nullvalue0/S100MotherboardV5/rescue-backup/S100-Backplane-2023-11-26-14-36-15.sch

## KiCad design rescue-backup/S100-Backplane-2023-11-26-14-36-15.sch (2023-12-12)

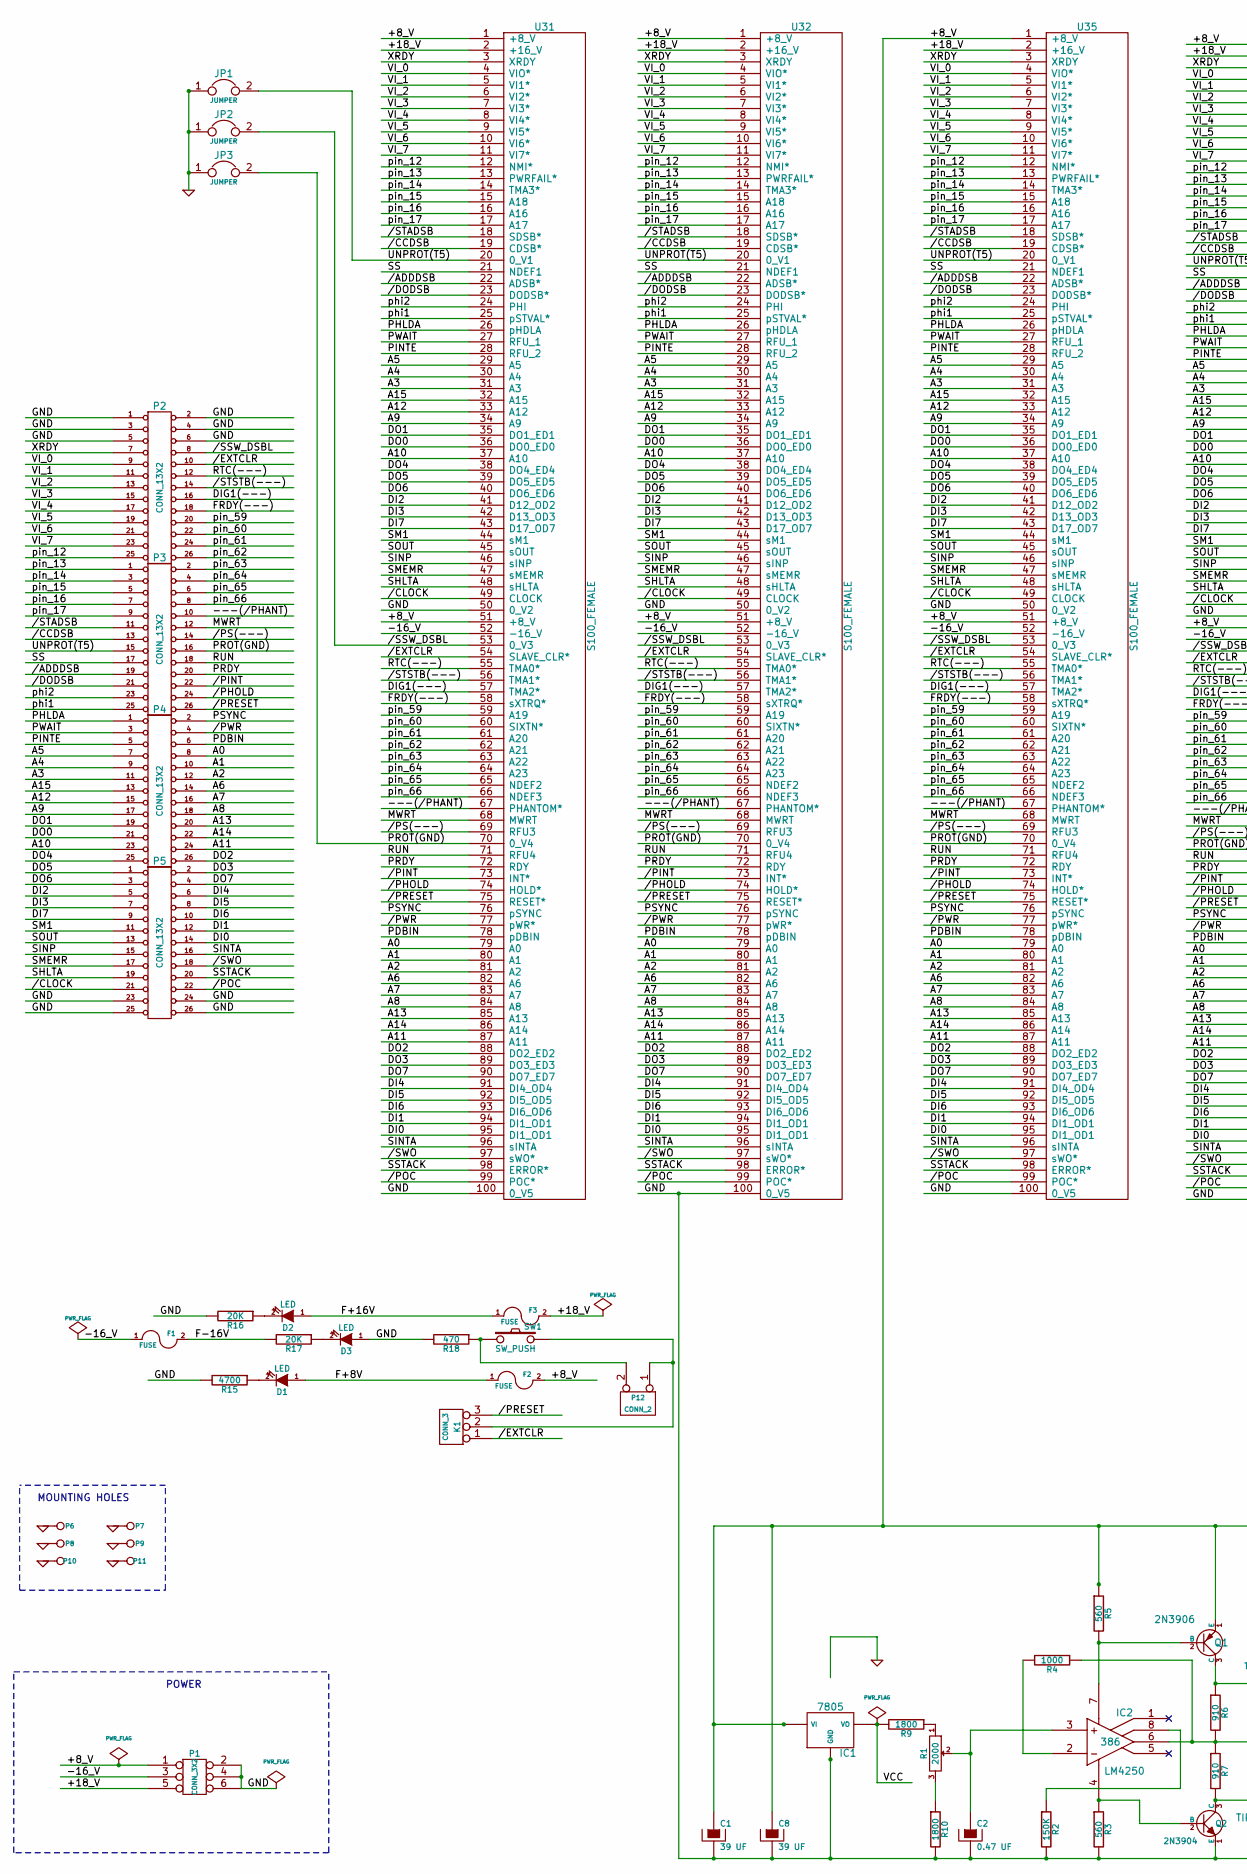
[picture p10: schematic S100-Backplane-2023-11-26-14-36-15.sch, part in row 1, column 1]

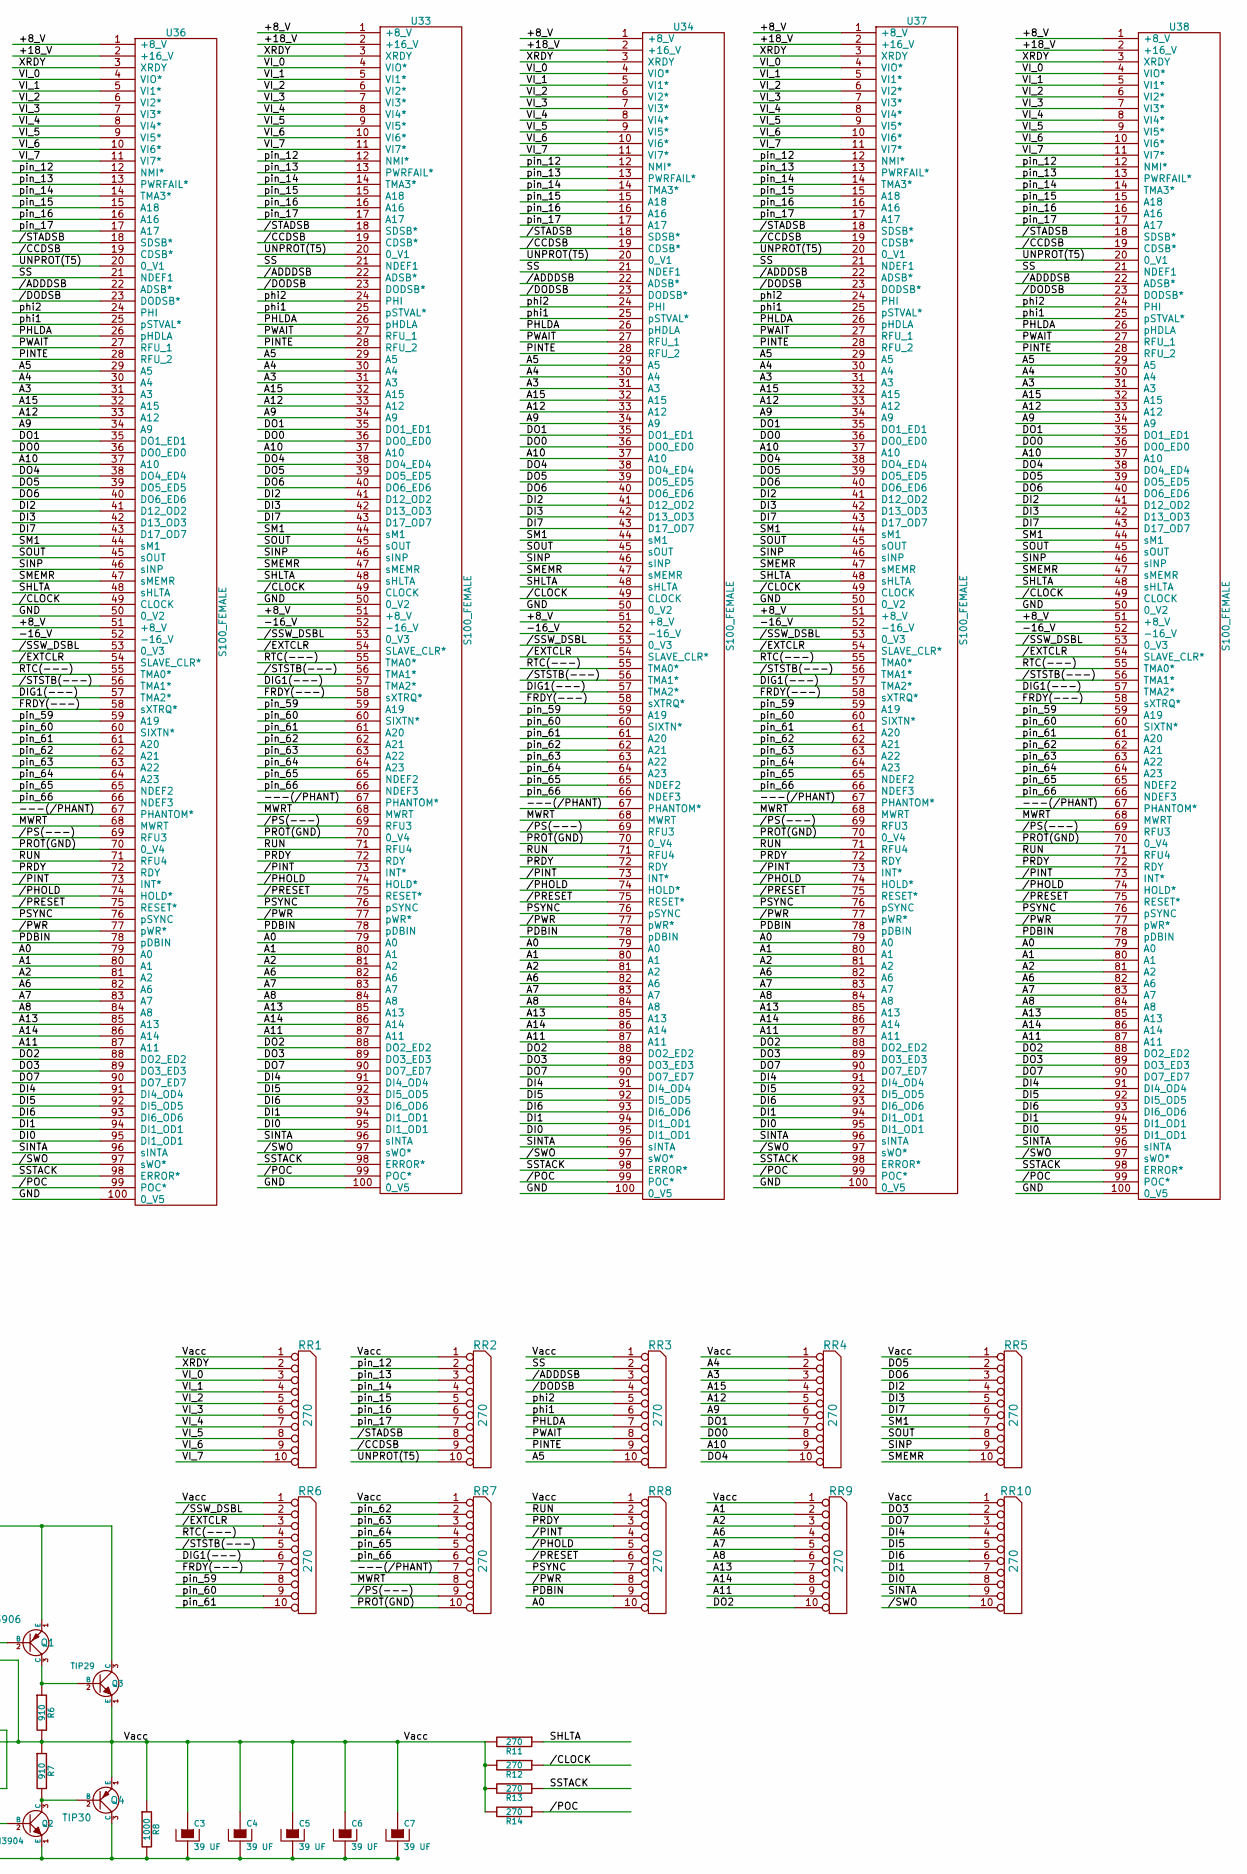
[picture p11: schematic S100-Backplane-2023-11-26-14-36-15.sch, part in row 1, column 2]

Parts:
C1, C3, C4, C5, C6, C7, C8: 39 UF; C1V7
C2: 0.47 UF; C1V7
D1, D2, D3: LED; LEDV
F1, F2, F3: FUSE; R5
IC1: 7805; LM78XX
IC2: LM4250; 8dip300
JP1, JP2, JP3: JUMPER; SIL-2
K1: CONN_3; PIN_ARRAY_3X1
P1: CONN_3X2; bornier6
P2, P3, P4, P5: CONN_13X2; pin_array_13x2
P6, P7, P8, P9, P10, P11: CONN_1; 1pin
P12: CONN_2; SIL-2
Q1: 2N3906; TO92
Q2: 2N3904; TO92-INVERT
Q3: TIP29; TO220
Q4: TIP30; TO220
R1: 2000; RV2
R2: 150K; R3
R3, R5: 560; R3
R4, R8: 1000; R3
R6, R7: 910; R3
R9, R10: 1800; R3
R11, R12, R13, R14: 270; R3
R15: 4700; R3
R16, R17: 20K; R3
R18: 470; R3
RR1, RR2, RR3, RR4, RR5, RR6, RR7, RR8, RR9, RR10: 270; r_pack9
SW1: SW_PUSH; SW_PUSH_SMALL
U31, U32, U33, U34, U35, U36, U37, U38: S100_FEMALE

Connections:
+8_V: C1.1, C8.1, F2.2, IC1.VI, P1.1, Q1.1 (E), Q3.3 (C), R5.1, U31.1 (+8_V), U31.51 (+8_V), U32.1 (+8_V), U32.51 (+8_V), U33.1 (+8_V), U33.51 (+8_V), U34.1 (+8_V), U34.51 (+8_V), U35.1 (+8_V), U35.51 (+8_V), U36.1 (+8_V), U36.51 (+8_V), U37.1 (+8_V), U37.51 (+8_V), U38.1 (+8_V), U38.51 (+8_V)
+18_V: F3.2, P1.5, U31.2 (+16_V), U32.2 (+16_V), U33.2 (+16_V), U34.2 (+16_V), U35.2 (+16_V), U36.2 (+16_V), U37.2 (+16_V), U38.2 (+16_V)
-16_V: F1.1, P1.3, U31.52 (-16_V), U32.52 (-16_V), U33.52 (-16_V), U34.52 (-16_V), U35.52 (-16_V), U36.52 (-16_V), U37.52 (-16_V), U38.52 (-16_V)
---(/PHANT): P3.10, RR7.7, U31.67 (PHANTOM*), U32.67 (PHANTOM*), U33.67 (PHANTOM*), U34.67 (PHANTOM*), U35.67 (PHANTOM*), U36.67 (PHANTOM*), U37.67 (PHANTOM*), U38.67 (PHANTOM*)
/ADDDSB: P3.19, RR3.3, U31.22 (ADSB*), U32.22 (ADSB*), U33.22 (ADSB*), U34.22 (ADSB*), U35.22 (ADSB*), U36.22 (ADSB*), U37.22 (ADSB*), U38.22 (ADSB*)
/CCDSB: P3.13, RR2.9, U31.19 (CDSB*), U32.19 (CDSB*), U33.19 (CDSB*), U34.19 (CDSB*), U35.19 (CDSB*), U36.19 (CDSB*), U37.19 (CDSB*), U38.19 (CDSB*)
/CLOCK: P5.21, R12.1, U31.49 (CLOCK), U32.49 (CLOCK), U33.49 (CLOCK), U34.49 (CLOCK), U35.49 (CLOCK), U36.49 (CLOCK), U37.49 (CLOCK), U38.49 (CLOCK)
/DODSB: P3.21, RR3.4, U31.23 (DODSB*), U32.23 (DODSB*), U33.23 (DODSB*), U34.23 (DODSB*), U35.23 (DODSB*), U36.23 (DODSB*), U37.23 (DODSB*), U38.23 (DODSB*)
/EXTCLR: K1.1, P2.10, RR6.3, U31.54 (SLAVE_CLR*), U32.54 (SLAVE_CLR*), U33.54 (SLAVE_CLR*), U34.54 (SLAVE_CLR*), U35.54 (SLAVE_CLR*), U36.54 (SLAVE_CLR*), U37.54 (SLAVE_CLR*), U38.54 (SLAVE_CLR*)
/PHOLD: P3.24 (P20), RR8.5, U31.74 (HOLD*), U32.74 (HOLD*), U33.74 (HOLD*), U34.74 (HOLD*), U35.74 (HOLD*), U36.74 (HOLD*), U37.74 (HOLD*), U38.74 (HOLD*)
/PINT: P3.22, RR8.4, U31.73 (INT*), U32.73 (INT*), U33.73 (INT*), U34.73 (INT*), U35.73 (INT*), U36.73 (INT*), U37.73 (INT*), U38.73 (INT*)
/POC: P5.22, R14.1, U31.99 (POC*), U32.99 (POC*), U33.99 (POC*), U34.99 (POC*), U35.99 (POC*), U36.99 (POC*), U37.99 (POC*), U38.99 (POC*)
/PRESET: K1.3, P3.26 (P22), RR8.6, U31.75 (RESET*), U32.75 (RESET*), U33.75 (RESET*), U34.75 (RESET*), U35.75 (RESET*), U36.75 (RESET*), U37.75 (RESET*), U38.75 (RESET*)
/PS(---): P3.14, RR7.9, U31.69 (RFU3), U32.69 (RFU3), U33.69 (RFU3), U34.69 (RFU3), U35.69 (RFU3), U36.69 (RFU3), U37.69 (RFU3), U38.69 (RFU3)
/PWR: P4.4, RR8.8, U31.77 (pWR*), U32.77 (pWR*), U33.77 (pWR*), U34.77 (pWR*), U35.77 (pWR*), U36.77 (pWR*), U37.77 (pWR*), U38.77 (pWR*)
/SSW_DSBL: JP2.2, P2.8, RR6.2, U31.53 (0_V3), U32.53 (0_V3), U33.53 (0_V3), U34.53 (0_V3), U35.53 (0_V3), U36.53 (0_V3), U37.53 (0_V3), U38.53 (0_V3)
/STADSB: P3.11, RR2.8, U31.18 (SDSB*), U32.18 (SDSB*), U33.18 (SDSB*), U34.18 (SDSB*), U35.18 (SDSB*), U36.18 (SDSB*), U37.18 (SDSB*), U38.18 (SDSB*)
/STSTB(---): P2.14, RR6.5, U31.56 (TMA1*), U32.56 (TMA1*), U33.56 (TMA1*), U34.56 (TMA1*), U35.56 (TMA1*), U36.56 (TMA1*), U37.56 (TMA1*), U38.56 (TMA1*)
/SWO: P5.18, RR10.10, U31.97 (sWO*), U32.97 (sWO*), U33.97 (sWO*), U34.97 (sWO*), U35.97 (sWO*), U36.97 (sWO*), U37.97 (sWO*), U38.97 (sWO*)
A0: P4.8, RR8.10, U31.79 (A0), U32.79 (A0), U33.79 (A0), U34.79 (A0), U35.79 (A0), U36.79 (A0), U37.79 (A0), U38.79 (A0)
A1: P4.10, RR9.2, U31.80 (A1), U32.80 (A1), U33.80 (A1), U34.80 (A1), U35.80 (A1), U36.80 (A1), U37.80 (A1), U38.80 (A1)
A2: P4.12, RR9.3, U31.81 (A2), U32.81 (A2), U33.81 (A2), U34.81 (A2), U35.81 (A2), U36.81 (A2), U37.81 (A2), U38.81 (A2)
A3: P4.11, RR4.3, U31.31 (A3), U32.31 (A3), U33.31 (A3), U34.31 (A3), U35.31 (A3), U36.31 (A3), U37.31 (A3), U38.31 (A3)
A4: P4.9, RR4.2, U31.30 (A4), U32.30 (A4), U33.30 (A4), U34.30 (A4), U35.30 (A4), U36.30 (A4), U37.30 (A4), U38.30 (A4)
A5: P4.7, RR3.10, U31.29 (A5), U32.29 (A5), U33.29 (A5), U34.29 (A5), U35.29 (A5), U36.29 (A5), U37.29 (A5), U38.29 (A5)
A6: P4.14, RR9.4, U31.82 (A6), U32.82 (A6), U33.82 (A6), U34.82 (A6), U35.82 (A6), U36.82 (A6), U37.82 (A6), U38.82 (A6)
A7: P4.16, RR9.5, U31.83 (A7), U32.83 (A7), U33.83 (A7), U34.83 (A7), U35.83 (A7), U36.83 (A7), U37.83 (A7), U38.83 (A7)
A8: P4.18, RR9.6, U31.84 (A8), U32.84 (A8), U33.84 (A8), U34.84 (A8), U35.84 (A8), U36.84 (A8), U37.84 (A8), U38.84 (A8)
A9: P4.17, RR4.6, U31.34 (A9), U32.34 (A9), U33.34 (A9), U34.34 (A9), U35.34 (A9), U36.34 (A9), U37.34 (A9), U38.34 (A9)
A10: P4.23, RR4.9, U31.37 (A10), U32.37 (A10), U33.37 (A10), U34.37 (A10), U35.37 (A10), U36.37 (A10), U37.37 (A10), U38.37 (A10)
A11: P4.24 (P20), RR9.9, U31.87 (A11), U32.87 (A11), U33.87 (A11), U34.87 (A11), U35.87 (A11), U36.87 (A11), U37.87 (A11), U38.87 (A11)
A12: P4.15, RR4.5, U31.33 (A12), U32.33 (A12), U33.33 (A12), U34.33 (A12), U35.33 (A12), U36.33 (A12), U37.33 (A12), U38.33 (A12)
A13: P4.20, RR9.7, U31.85 (A13), U32.85 (A13), U33.85 (A13), U34.85 (A13), U35.85 (A13), U36.85 (A13), U37.85 (A13), U38.85 (A13)
A14: P4.22, RR9.8, U31.86 (A14), U32.86 (A14), U33.86 (A14), U34.86 (A14), U35.86 (A14), U36.86 (A14), U37.86 (A14), U38.86 (A14)
A15: P4.13, RR4.4, U31.32 (A15), U32.32 (A15), U33.32 (A15), U34.32 (A15), U35.32 (A15), U36.32 (A15), U37.32 (A15), U38.32 (A15)
DI0: P5.14, RR10.8, U31.95 (DI1_OD1), U32.95 (DI1_OD1), U33.95 (DI1_OD1), U34.95 (DI1_OD1), U35.95 (DI1_OD1), U36.95 (DI1_OD1), U37.95 (DI1_OD1), U38.95 (DI1_OD1)
DI1: P5.12, RR10.7, U31.94 (DI1_OD1), U32.94 (DI1_OD1), U33.94 (DI1_OD1), U34.94 (DI1_OD1), U35.94 (DI1_OD1), U36.94 (DI1_OD1), U37.94 (DI1_OD1), U38.94 (DI1_OD1)
DI2: P5.5, RR5.4, U31.41 (D12_OD2), U32.41 (D12_OD2), U33.41 (D12_OD2), U34.41 (D12_OD2), U35.41 (D12_OD2), U36.41 (D12_OD2), U37.41 (D12_OD2), U38.41 (D12_OD2)
DI3: P5.7, RR5.5, U31.42 (D13_OD3), U32.42 (D13_OD3), U33.42 (D13_OD3), U34.42 (D13_OD3), U35.42 (D13_OD3), U36.42 (D13_OD3), U37.42 (D13_OD3), U38.42 (D13_OD3)
DI4: P5.6, RR10.4, U31.91 (DI4_OD4), U32.91 (DI4_OD4), U33.91 (DI4_OD4), U34.91 (DI4_OD4), U35.91 (DI4_OD4), U36.91 (DI4_OD4), U37.91 (DI4_OD4), U38.91 (DI4_OD4)
DI5: P5.8, RR10.5, U31.92 (DI5_OD5), U32.92 (DI5_OD5), U33.92 (DI5_OD5), U34.92 (DI5_OD5), U35.92 (DI5_OD5), U36.92 (DI5_OD5), U37.92 (DI5_OD5), U38.92 (DI5_OD5)
DI6: P5.10, RR10.6, U31.93 (DI6_OD6), U32.93 (DI6_OD6), U33.93 (DI6_OD6), U34.93 (DI6_OD6), U35.93 (DI6_OD6), U36.93 (DI6_OD6), U37.93 (DI6_OD6), U38.93 (DI6_OD6)
DI7: P5.9, RR5.6, U31.43 (D17_OD7), U32.43 (D17_OD7), U33.43 (D17_OD7), U34.43 (D17_OD7), U35.43 (D17_OD7), U36.43 (D17_OD7), U37.43 (D17_OD7), U38.43 (D17_OD7)
DIG1(---): P2.16, RR6.6, U31.57 (TMA2*), U32.57 (TMA2*), U33.57 (TMA2*), U34.57 (TMA2*), U35.57 (TMA2*), U36.57 (TMA2*), U37.57 (TMA2*), U38.57 (TMA2*)
DO0: P4.21, RR4.8, U31.36 (DO0_ED0), U32.36 (DO0_ED0), U33.36 (DO0_ED0), U34.36 (DO0_ED0), U35.36 (DO0_ED0), U36.36 (DO0_ED0), U37.36 (DO0_ED0), U38.36 (DO0_ED0)
DO1: P4.19, RR4.7, U31.35 (DO1_ED1), U32.35 (DO1_ED1), U33.35 (DO1_ED1), U34.35 (DO1_ED1), U35.35 (DO1_ED1), U36.35 (DO1_ED1), U37.35 (DO1_ED1), U38.35 (DO1_ED1)
DO2: P4.26 (P22), RR9.10, U31.88 (DO2_ED2), U32.88 (DO2_ED2), U33.88 (DO2_ED2), U34.88 (DO2_ED2), U35.88 (DO2_ED2), U36.88 (DO2_ED2), U37.88 (DO2_ED2), U38.88 (DO2_ED2)
DO3: P5.2, RR10.2, U31.89 (DO3_ED3), U32.89 (DO3_ED3), U33.89 (DO3_ED3), U34.89 (DO3_ED3), U35.89 (DO3_ED3), U36.89 (DO3_ED3), U37.89 (DO3_ED3), U38.89 (DO3_ED3)
DO4: P4.25 (P24), RR4.10, U31.38 (DO4_ED4), U32.38 (DO4_ED4), U33.38 (DO4_ED4), U34.38 (DO4_ED4), U35.38 (DO4_ED4), U36.38 (DO4_ED4), U37.38 (DO4_ED4), U38.38 (DO4_ED4)
DO5: P5.1, RR5.2, U31.39 (DO5_ED5), U32.39 (DO5_ED5), U33.39 (DO5_ED5), U34.39 (DO5_ED5), U35.39 (DO5_ED5), U36.39 (DO5_ED5), U37.39 (DO5_ED5), U38.39 (DO5_ED5)
DO6: P5.3, RR5.3, U31.40 (DO6_ED6), U32.40 (DO6_ED6), U33.40 (DO6_ED6), U34.40 (DO6_ED6), U35.40 (DO6_ED6), U36.40 (DO6_ED6), U37.40 (DO6_ED6), U38.40 (DO6_ED6)
DO7: P5.4, RR10.3, U31.90 (DO7_ED7), U32.90 (DO7_ED7), U33.90 (DO7_ED7), U34.90 (DO7_ED7), U35.90 (DO7_ED7), U36.90 (DO7_ED7), U37.90 (DO7_ED7), U38.90 (DO7_ED7)
F+8V: D1.1 (A), F2.1
F+16V: D2.1 (A), F3.1
F-16V: F1.2, R17.2
FRDY(---): P2.18, RR6.7, U31.58 (sXTRQ*), U32.58 (sXTRQ*), U33.58 (sXTRQ*), U34.58 (sXTRQ*), U35.58 (sXTRQ*), U36.58 (sXTRQ*), U37.58 (sXTRQ*), U38.58 (sXTRQ*)
GND: C1.2, C2.2, C3.2, C4.2, C5.2, C6.2, C7.2, C8.2, D3.1 (A), IC1.GND, JP1.1, JP2.1, JP3.1, P1.2, P1.4, P1.6, P2.1, P2.2, P2.3, P2.4, P2.5, P2.6, P5.23, P5.24 (P20), P5.25 (P24), P5.26 (P22), P6.1, P7.1, P8.1, P9.1, P10.1, P11.1, Q2.1 (E), Q4.3 (C), R2.2, R3.2, R8.2, R10.2, R15.2, R16.2, R18.2, U31.50 (0_V2), U31.100 (0_V5), U32.50 (0_V2), U32.100 (0_V5), U33.50 (0_V2), U33.100 (0_V5), U34.50 (0_V2), U34.100 (0_V5), U35.50 (0_V2), U35.100 (0_V5), U36.50 (0_V2), U36.100 (0_V5), U37.50 (0_V2), U37.100 (0_V5), U38.50 (0_V2), U38.100 (0_V5)
MWRT: P3.12, RR7.8, U31.68 (MWRT), U32.68 (MWRT), U33.68 (MWRT), U34.68 (MWRT), U35.68 (MWRT), U36.68 (MWRT), U37.68 (MWRT), U38.68 (MWRT)
unnamed: C2.1, IC2.3 (PLUS), R1.2
unnamed: D1.2 (K), R15.1
unnamed: D2.2 (K), R16.1
unnamed: D3.2 (K), R17.1
unnamed: IC2.2 (MINUS), R4.2
unnamed: IC2.4 (MINUS), Q2.2 (B), R3.1
unnamed: IC2.7 (PLUS), Q1.2 (B), R5.2
unnamed: IC2.8 (FIN), R2.1
unnamed: K1.2 (PM), P12.1, SW1.2
unnamed: P12.2 (PM), R18.1, SW1.1
unnamed: Q1.3 (C), Q3.2 (B), R6.1
unnamed: Q2.3 (C), Q4.2 (B), R7.2
unnamed: R1.1, R9.1
unnamed: R1.3, R10.1
PDBIN: P4.6, RR8.9, U31.78 (pDBIN), U32.78 (pDBIN), U33.78 (pDBIN), U34.78 (pDBIN), U35.78 (pDBIN), U36.78 (pDBIN), U37.78 (pDBIN), U38.78 (pDBIN)
PHLDA: P4.1, RR3.7, U31.26 (pHDLA), U32.26 (pHDLA), U33.26 (pHDLA), U34.26 (pHDLA), U35.26 (pHDLA), U36.26 (pHDLA), U37.26 (pHDLA), U38.26 (pHDLA)
PINTE: P4.5, RR3.9, U31.28 (RFU_2), U32.28 (RFU_2), U33.28 (RFU_2), U34.28 (RFU_2), U35.28 (RFU_2), U36.28 (RFU_2), U37.28 (RFU_2), U38.28 (RFU_2)
PRDY: P3.20, RR8.3, U31.72 (RDY), U32.72 (RDY), U33.72 (RDY), U34.72 (RDY), U35.72 (RDY), U36.72 (RDY), U37.72 (RDY), U38.72 (RDY)
PROT(GND): JP3.2, P3.16, RR7.10, U31.70 (0_V4), U32.70 (0_V4), U33.70 (0_V4), U34.70 (0_V4), U35.70 (0_V4), U36.70 (0_V4), U37.70 (0_V4), U38.70 (0_V4)
PSYNC: P4.2, RR8.7, U31.76 (pSYNC), U32.76 (pSYNC), U33.76 (pSYNC), U34.76 (pSYNC), U35.76 (pSYNC), U36.76 (pSYNC), U37.76 (pSYNC), U38.76 (pSYNC)
PWAIT: P4.3, RR3.8, U31.27 (RFU_1), U32.27 (RFU_1), U33.27 (RFU_1), U34.27 (RFU_1), U35.27 (RFU_1), U36.27 (RFU_1), U37.27 (RFU_1), U38.27 (RFU_1)
RTC(---): P2.12, RR6.4, U31.55 (TMA0*), U32.55 (TMA0*), U33.55 (TMA0*), U34.55 (TMA0*), U35.55 (TMA0*), U36.55 (TMA0*), U37.55 (TMA0*), U38.55 (TMA0*)
RUN: P3.18, RR8.2, U31.71 (RFU4), U32.71 (RFU4), U33.71 (RFU4), U34.71 (RFU4), U35.71 (RFU4), U36.71 (RFU4), U37.71 (RFU4), U38.71 (RFU4)
SHLTA: P5.19, R11.1, U31.48 (sHLTA), U32.48 (sHLTA), U33.48 (sHLTA), U34.48 (sHLTA), U35.48 (sHLTA), U36.48 (sHLTA), U37.48 (sHLTA), U38.48 (sHLTA)
SINP: P5.15, RR5.9, U31.46 (sINP), U32.46 (sINP), U33.46 (sINP), U34.46 (sINP), U35.46 (sINP), U36.46 (sINP), U37.46 (sINP), U38.46 (sINP)
SINTA: P5.16, RR10.9, U31.96 (sINTA), U32.96 (sINTA), U33.96 (sINTA), U34.96 (sINTA), U35.96 (sINTA), U36.96 (sINTA), U37.96 (sINTA), U38.96 (sINTA)
SM1: P5.11, RR5.7, U31.44 (sM1), U32.44 (sM1), U33.44 (sM1), U34.44 (sM1), U35.44 (sM1), U36.44 (sM1), U37.44 (sM1), U38.44 (sM1)
SMEMR: P5.17, RR5.10, U31.47 (sMEMR), U32.47 (sMEMR), U33.47 (sMEMR), U34.47 (sMEMR), U35.47 (sMEMR), U36.47 (sMEMR), U37.47 (sMEMR), U38.47 (sMEMR)
SOUT: P5.13, RR5.8, U31.45 (sOUT), U32.45 (sOUT), U33.45 (sOUT), U34.45 (sOUT), U35.45 (sOUT), U36.45 (sOUT), U37.45 (sOUT), U38.45 (sOUT)
SS: P3.17, RR3.2, U31.21 (NDEF1), U32.21 (NDEF1), U33.21 (NDEF1), U34.21 (NDEF1), U35.21 (NDEF1), U36.21 (NDEF1), U37.21 (NDEF1), U38.21 (NDEF1)
SSTACK: P5.20, R13.1, U31.98 (ERROR*), U32.98 (ERROR*), U33.98 (ERROR*), U34.98 (ERROR*), U35.98 (ERROR*), U36.98 (ERROR*), U37.98 (ERROR*), U38.98 (ERROR*)
UNPROT(T5): JP1.2, P3.15, RR2.10, U31.20 (0_V1), U32.20 (0_V1), U33.20 (0_V1), U34.20 (0_V1), U35.20 (0_V1), U36.20 (0_V1), U37.20 (0_V1), U38.20 (0_V1)
VCC: IC1.VO, R9.2
VI_0: P2.9, RR1.3, U31.4 (VIO*), U32.4 (VIO*), U33.4 (VIO*), U34.4 (VIO*), U35.4 (VIO*), U36.4 (VIO*), U37.4 (VIO*), U38.4 (VIO*)
VI_1: P2.11, RR1.4, U31.5 (VI1*), U32.5 (VI1*), U33.5 (VI1*), U34.5 (VI1*), U35.5 (VI1*), U36.5 (VI1*), U37.5 (VI1*), U38.5 (VI1*)
VI_2: P2.13, RR1.5, U31.6 (VI2*), U32.6 (VI2*), U33.6 (VI2*), U34.6 (VI2*), U35.6 (VI2*), U36.6 (VI2*), U37.6 (VI2*), U38.6 (VI2*)
VI_3: P2.15, RR1.6, U31.7 (VI3*), U32.7 (VI3*), U33.7 (VI3*), U34.7 (VI3*), U35.7 (VI3*), U36.7 (VI3*), U37.7 (VI3*), U38.7 (VI3*)
VI_4: P2.17, RR1.7, U31.8 (VI4*), U32.8 (VI4*), U33.8 (VI4*), U34.8 (VI4*), U35.8 (VI4*), U36.8 (VI4*), U37.8 (VI4*), U38.8 (VI4*)
VI_5: P2.19, RR1.8, U31.9 (VI5*), U32.9 (VI5*), U33.9 (VI5*), U34.9 (VI5*), U35.9 (VI5*), U36.9 (VI5*), U37.9 (VI5*), U38.9 (VI5*)
VI_6: P2.21, RR1.9, U31.10 (VI6*), U32.10 (VI6*), U33.10 (VI6*), U34.10 (VI6*), U35.10 (VI6*), U36.10 (VI6*), U37.10 (VI6*), U38.10 (VI6*)
VI_7: P2.23, RR1.10, U31.11 (VI7*), U32.11 (VI7*), U33.11 (VI7*), U34.11 (VI7*), U35.11 (VI7*), U36.11 (VI7*), U37.11 (VI7*), U38.11 (VI7*)
Vacc: C3.1, C4.1, C5.1, C6.1, C7.1, IC2.6 (OUTPUT), Q3.1 (E), Q4.1 (E), R4.1, R6.2, R7.1, R8.1, R11.2, R12.2, R13.2, R14.2, RR1.1 (COM), RR2.1 (COM), RR3.1 (COM), RR4.1 (COM), RR5.1 (COM), RR6.1 (COM), RR7.1 (COM), RR8.1 (COM), RR9.1 (COM), RR10.1 (COM)
XRDY: P2.7, RR1.2, U31.3 (XRDY), U32.3 (XRDY), U33.3 (XRDY), U34.3 (XRDY), U35.3 (XRDY), U36.3 (XRDY), U37.3 (XRDY), U38.3 (XRDY)
phi1: P3.25 (P24), RR3.6, U31.25 (pSTVAL*), U32.25 (pSTVAL*), U33.25 (pSTVAL*), U34.25 (pSTVAL*), U35.25 (pSTVAL*), U36.25 (pSTVAL*), U37.25 (pSTVAL*), U38.25 (pSTVAL*)
phi2: P3.23, RR3.5, U31.24 (PHI), U32.24 (PHI), U33.24 (PHI), U34.24 (PHI), U35.24 (PHI), U36.24 (PHI), U37.24 (PHI), U38.24 (PHI)
pin_12: P2.25 (P24), RR2.2, U31.12 (NMI*), U32.12 (NMI*), U33.12 (NMI*), U34.12 (NMI*), U35.12 (NMI*), U36.12 (NMI*), U37.12 (NMI*), U38.12 (NMI*)
pin_13: P3.1, RR2.3, U31.13 (PWRFAIL*), U32.13 (PWRFAIL*), U33.13 (PWRFAIL*), U34.13 (PWRFAIL*), U35.13 (PWRFAIL*), U36.13 (PWRFAIL*), U37.13 (PWRFAIL*), U38.13 (PWRFAIL*)
pin_14: P3.3, RR2.4, U31.14 (TMA3*), U32.14 (TMA3*), U33.14 (TMA3*), U34.14 (TMA3*), U35.14 (TMA3*), U36.14 (TMA3*), U37.14 (TMA3*), U38.14 (TMA3*)
pin_15: P3.5, RR2.5, U31.15 (A18), U32.15 (A18), U33.15 (A18), U34.15 (A18), U35.15 (A18), U36.15 (A18), U37.15 (A18), U38.15 (A18)
pin_16: P3.7, RR2.6, U31.16 (A16), U32.16 (A16), U33.16 (A16), U34.16 (A16), U35.16 (A16), U36.16 (A16), U37.16 (A16), U38.16 (A16)
pin_17: P3.9, RR2.7, U31.17 (A17), U32.17 (A17), U33.17 (A17), U34.17 (A17), U35.17 (A17), U36.17 (A17), U37.17 (A17), U38.17 (A17)
pin_59: P2.20, RR6.8, U31.59 (A19), U32.59 (A19), U33.59 (A19), U34.59 (A19), U35.59 (A19), U36.59 (A19), U37.59 (A19), U38.59 (A19)
pin_60: P2.22, RR6.9, U31.60 (SIXTN*), U32.60 (SIXTN*), U33.60 (SIXTN*), U34.60 (SIXTN*), U35.60 (SIXTN*), U36.60 (SIXTN*), U37.60 (SIXTN*), U38.60 (SIXTN*)
pin_61: P2.24 (P20), RR6.10, U31.61 (A20), U32.61 (A20), U33.61 (A20), U34.61 (A20), U35.61 (A20), U36.61 (A20), U37.61 (A20), U38.61 (A20)
pin_62: P2.26 (P22), RR7.2, U31.62 (A21), U32.62 (A21), U33.62 (A21), U34.62 (A21), U35.62 (A21), U36.62 (A21), U37.62 (A21), U38.62 (A21)
pin_63: P3.2, RR7.3, U31.63 (A22), U32.63 (A22), U33.63 (A22), U34.63 (A22), U35.63 (A22), U36.63 (A22), U37.63 (A22), U38.63 (A22)
pin_64: P3.4, RR7.4, U31.64 (A23), U32.64 (A23), U33.64 (A23), U34.64 (A23), U35.64 (A23), U36.64 (A23), U37.64 (A23), U38.64 (A23)
pin_65: P3.6, RR7.5, U31.65 (NDEF2), U32.65 (NDEF2), U33.65 (NDEF2), U34.65 (NDEF2), U35.65 (NDEF2), U36.65 (NDEF2), U37.65 (NDEF2), U38.65 (NDEF2)
pin_66: P3.8, RR7.6, U31.66 (NDEF3), U32.66 (NDEF3), U33.66 (NDEF3), U34.66 (NDEF3), U35.66 (NDEF3), U36.66 (NDEF3), U37.66 (NDEF3), U38.66 (NDEF3)

Notes on the sheet:
MOUNTING HOLES
POWER
